clowrey/isoSPI-M3Y-BMS-PCB/graphics/image0.jpg

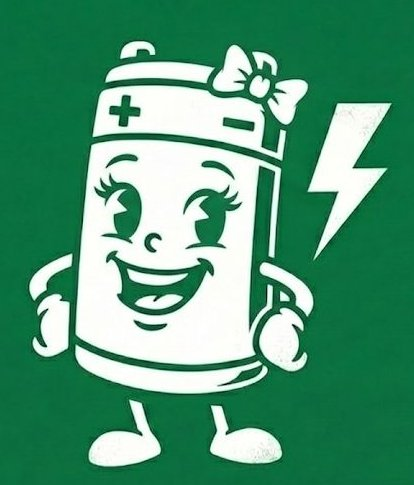
graphics/image0.jpg
